adafruit/Adafruit-ICM20948-PCB/assets/4554.jpg

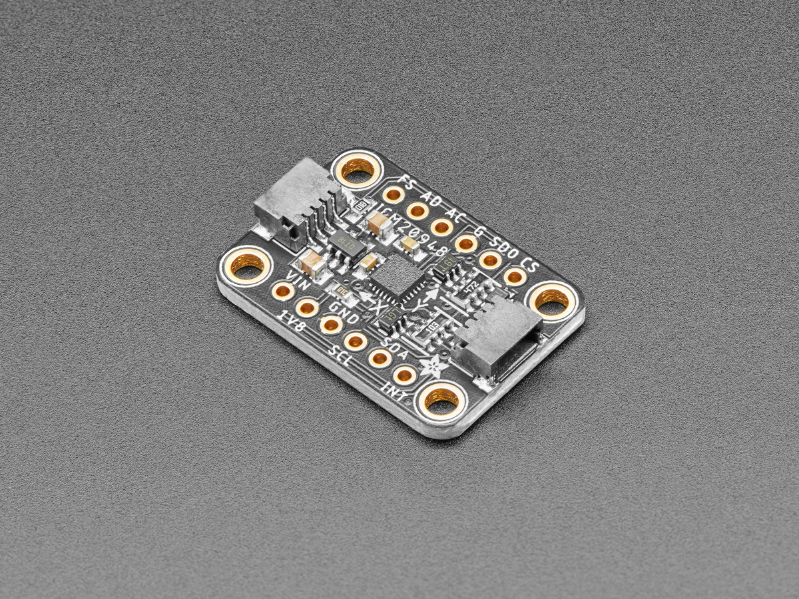
assets/4554.jpg
